trebb/iso50/firmware-pcb/config.h

/*
Copyright 2012 Jun Wako <wakojun@gmail.com>

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
You should have received a copy of the GNU General Public License
along with this program.  If not, see <http://www.gnu.org/licenses/>.
*/

#ifndef CONFIG_H
#define CONFIG_H


/* USB Device descriptor parameter */
#define VENDOR_ID 0x1209
#define PRODUCT_ID 0x5050
/* (Thanks to http://pid.codes) */
#define DEVICE_VER 0x0001
#define MANUFACTURER trebb
#define PRODUCT ISO50
#define DESCRIPTION TMK keyboard firmware for ISO50

/* key matrix size */
#define MATRIX_ROWS 4
#define MATRIX_COLS 14

/* define if matrix has ghost */
//#define MATRIX_HAS_GHOST

/* Set 0 if debouncing isn't needed */
#define DEBOUNCE 5

/*
 * Feature disable options
 *  These options are also useful to firmware size reduction.
 */

/* disable debug print */
#define NO_DEBUG

/* disable print */
#define NO_PRINT

/* disable action features */
//#define NO_ACTION_LAYER
//#define NO_ACTION_TAPPING
#define NO_ACTION_ONESHOT
#define NO_ACTION_MACRO
//#define NO_ACTION_FUNCTION

#endif
