trebb/iso50/firmware-pcb/keymap_common.h

/*
Copyright 2012,2013 Jun Wako <wakojun@gmail.com>

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
You should have received a copy of the GNU General Public License
along with this program.  If not, see <http://www.gnu.org/licenses/>.
*/
#ifndef KEYMAP_COMMON_H
#define KEYMAP_COMMON_H

#include <stdint.h>
#include <stdbool.h>
#include <avr/pgmspace.h>
#include "action_layer.h"
#include "action_util.h"


extern const uint8_t keymaps[][MATRIX_ROWS][MATRIX_COLS];
extern const uint16_t fn_actions[];


/* ISO50 keymap definition macro
 * Layout: 52key
 * ,-----------------------------------------------------------.
 * |Esc  |  Q|  W|  E|  R|  T|  Y|  U|  I|  O|  P|  [|  ]|     |
 * |------------------------------------------------------.En- |
 * |Tab   |  A|  S|  D|  F|  G|  H|  J|  K|  L|  ;|  '|  #|ter |
 * |-----------------------------------------------------------|
 * |Shft|  \|  Z|  X|  C|  V|  B|  N|  M|  ,|  .|  /|Shift|Bksp|
 * |-----------------------------------------------------------|
 * |Ctrl|Supr| Alt | Num | Nav |      Rat|AltGr|Super|Menu|Ctrl|
 * `-----------------------------------------------------------'
 */
#define KEYMAP(                                                         \
    K00, K01, K02, K03, K04, K05, K06, K07, K08, K09, K0A, K0B, K0C,    \
    K10, K11, K12, K13, K14, K15, K16, K17, K18, K19, K1A, K1B, K1C, K1D, \
    K20, K21, K22, K23, K24, K25, K26, K27, K28, K29, K2A, K2B, K2C, K2D, \
    K30, K31, K32,      K34, K35,      K37, K38,      K3A, K3B, K3C, K3D \
    ) {                                                                 \
    { KC_##K00, KC_##K01, KC_##K02, KC_##K03, KC_##K04, KC_##K05, KC_##K06, KC_##K07, KC_##K08, KC_##K09, KC_##K0A, KC_##K0B, KC_##K0C, KC_NO }, \
    { KC_##K10, KC_##K11, KC_##K12, KC_##K13, KC_##K14, KC_##K15, KC_##K16, KC_##K17, KC_##K18, KC_##K19, KC_##K1A, KC_##K1B, KC_##K1C, KC_##K1D }, \
    { KC_##K20, KC_##K21, KC_##K22, KC_##K23, KC_##K24, KC_##K25, KC_##K26, KC_##K27, KC_##K28, KC_##K29, KC_##K2A, KC_##K2B, KC_##K2C, KC_##K2D }, \
    { KC_##K30, KC_##K31, KC_##K32, KC_NO,    KC_##K34, KC_##K35, KC_NO,    KC_##K37, KC_##K38, KC_NO,    KC_##K3A, KC_##K3B, KC_##K3C, KC_##K3D } \
}

#endif
